tubbytwins/bumwings-kbd/v001/pcb_core52840/bumwings_v001_core.kicad_sch

## KiCad design v001/pcb_core52840/bumwings_v001_core.kicad_sch (2022-12-24)

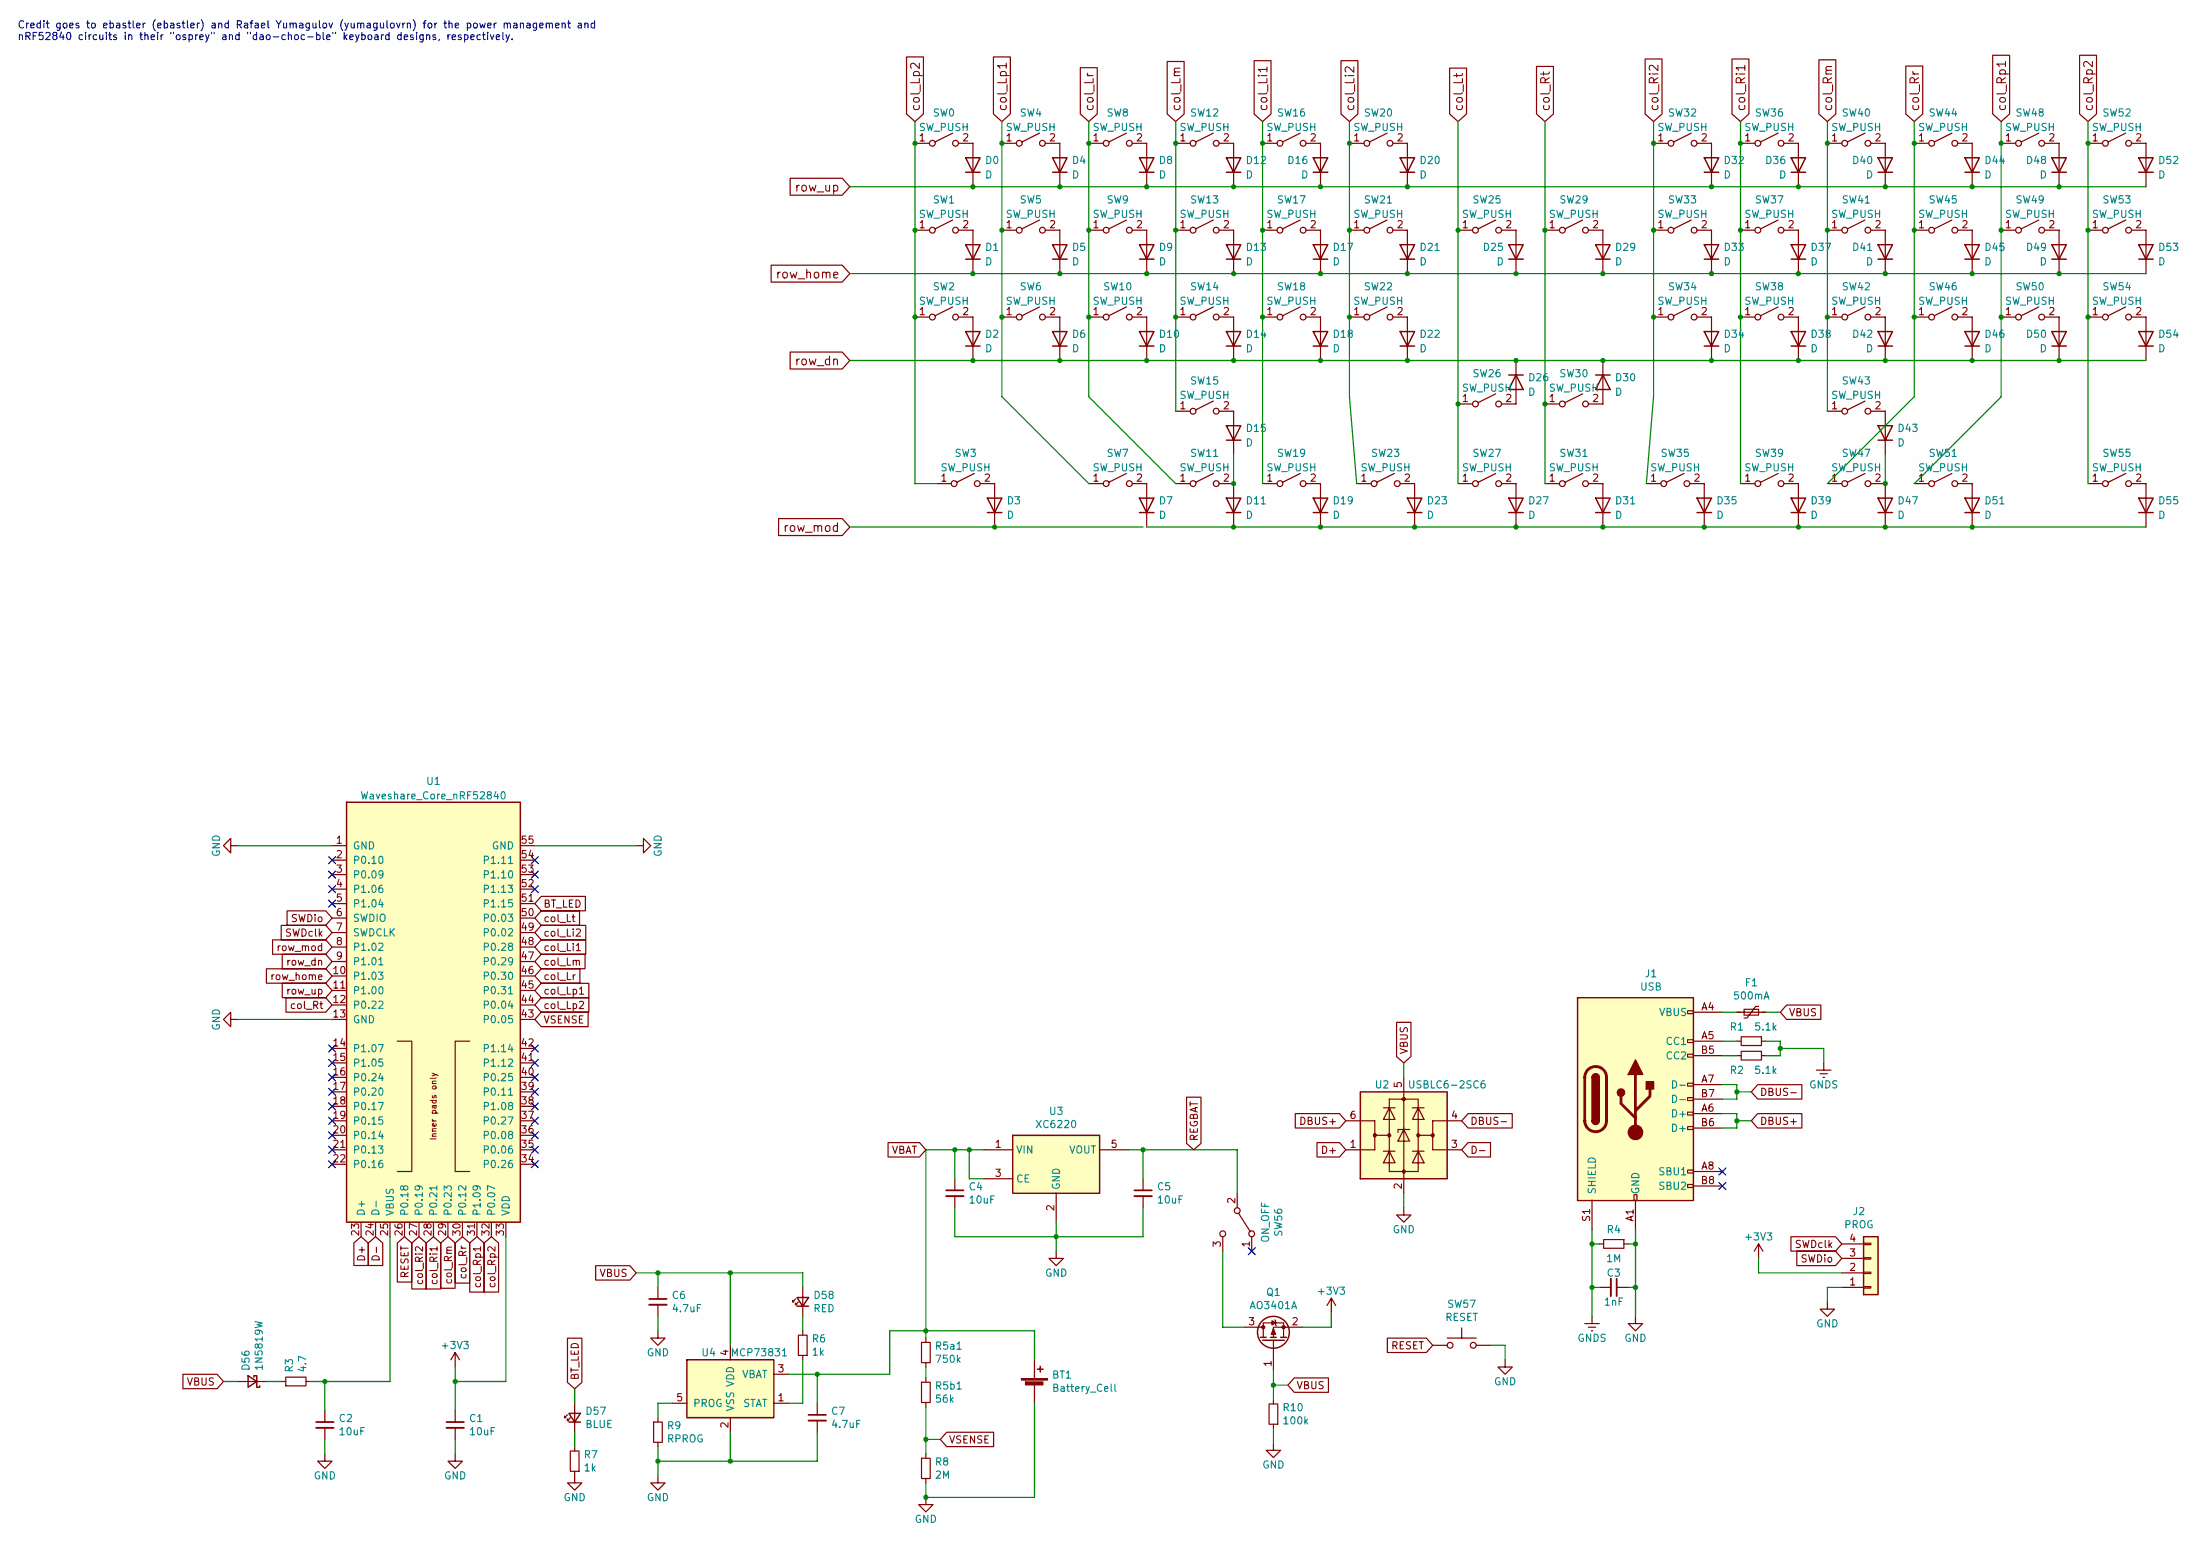
[picture p16: schematic bumwings_v001_core.kicad_sch]

Parts:
BT1: Battery_Cell; Battery
C1, C2, C4, C5: 10uF; C_1206_3216Metric_Pad1.33x1.80mm_HandSolder; LCSC C19702
C3: 1nF; C_1206_3216Metric_Pad1.33x1.80mm_HandSolder; LCSC C1588
C6, C7: 4.7uF; C_1206_3216Metric_Pad1.33x1.80mm_HandSolder; LCSC C19666
D0, D1, D2, D3, D4, D5, D6, D7, D8, D9, D10, D11, D12, D13, D14, D15, D16, D17, D18, D19, D20, D21, D22, D23, D25, D26, D27, D29, D30, D31, D32, D33, D34, D35, D36, D37, D38, D39, D40, D41, D42, D43, D44, D45, D46, D47, D48, D49, D50, D51, D52, D53, D54, D55: D; Diode_D_SOD-123
D56: 1N5819W; D_SOD-123; LCSC C169540
D57: BLUE; LED_1206_3216Metric_Pad1.42x1.75mm_HandSolder; LCSC C72041
D58: RED; LED_1206_3216Metric_Pad1.42x1.75mm_HandSolder; LCSC C2286
F1: 500mA; Fuse_1206_3216Metric_Pad1.42x1.75mm_HandSolder; LCSC C355568
J1: USB; USB-C_C168688; LCSC C168688
J2: PROG
Q1: AO3401A; SOT-23; LCSC C15127
R1, R2: 5.1k; R_1206_3216Metric_Pad1.30x1.75mm_HandSolder; LCSC C23186
R3: 4.7; R_1206_3216Metric_Pad1.30x1.75mm_HandSolder; LCSC C23164
R4: 1M; R_1206_3216Metric_Pad1.30x1.75mm_HandSolder; LCSC C22935
R5a1: 750k; R_1206_3216Metric_Pad1.30x1.75mm_HandSolder; LCSC C103828
R5b1: 56k; R_1206_3216Metric_Pad1.30x1.75mm_HandSolder; LCSC C103828
R6, R7: 1k; R_1206_3216Metric_Pad1.30x1.75mm_HandSolder; LCSC C21190
R8: 2M; R_1206_3216Metric_Pad1.30x1.75mm_HandSolder; LCSC C22976
R9: RPROG; R_1206_3216Metric_Pad1.30x1.75mm_HandSolder; LCSC C22978
R10: 100k; R_1206_3216Metric_Pad1.30x1.75mm_HandSolder; LCSC C25803
SW0, SW1, SW2, SW4, SW5, SW6, SW7, SW8, SW9, SW10, SW11, SW12, SW13, SW14, SW15, SW16, SW17, SW18, SW19, SW20, SW21, SW22, SW26, SW30, SW32, SW33, SW34, SW36, SW37, SW38, SW39, SW40, SW41, SW42, SW43, SW44, SW45, SW46, SW47, SW48, SW49, SW50, SW51, SW52, SW53, SW54: SW_PUSH; Kailh_PG1350_1u_hotswap
SW3, SW25, SW27, SW29, SW31, SW55: SW_PUSH; Kailh_PG1350_1.5u_hotswap
SW23, SW35: SW_PUSH; Kailh_PG1350_2u_stab_hotswap
SW56: ON_OFF; MSK-12C02; LCSC C431541
SW57: RESET; TS-1086E; LCSC C455276
U1: Waveshare_Core_nRF52840; Core_nRF52840
U2: USBLC6-2SC6; SOT-23-6; LCSC C558442
U3: XC6220; SOT-23-5; LCSC C86534
U4: MCP73831; SOT-23-5; LCSC C14879

Connections:
+3V3: C1.1, J2.2, Q1.2 (S), U1.33 (VDD)
BT_LED: D57.2 (A), U1.51 (P1.15)
D+: U1.23 (D+), U2.1 (I/O1)
D-: U1.24 (D-), U2.3 (I/O2)
DBUS+: J1.A6 (D+), J1.B6 (D+), U2.6 (I/O1)
DBUS-: J1.A7 (D-), J1.B7 (D-), U2.4 (I/O2)
GND: BT1.2 (-), C1.2, C2.2, C3.1, C4.2, C5.2, C6.2, C7.2, J1.A1 (GND), J1.A12 (GND), J1.B1 (GND), J1.B12 (GND), J2.1, R4.1, R7.1, R8.2, R9.2, R10.1, SW57.2, U1.1 (GND), U1.13 (GND), U1.55 (GND), U2.2 (GND), U3.2 (GND), U4.2 (VSS)
GNDS: C3.2, J1.S1 (SHIELD), R1.1, R2.1, R4.2
unnamed: C2.1, R3.2, U1.25 (VBUS)
unnamed: D0.2 (A), SW0.2 (B)
unnamed: D1.2 (A), SW1.2 (B)
unnamed: D2.2 (A), SW2.2 (B)
unnamed: D3.2 (A), SW3.2 (B)
unnamed: D4.2 (A), SW4.2 (B)
unnamed: D5.2 (A), SW5.2 (B)
unnamed: D6.2 (A), SW6.2 (B)
unnamed: D7.2 (A), SW7.2 (B)
unnamed: D8.2 (A), SW8.2 (B)
unnamed: D9.2 (A), SW9.2 (B)
unnamed: D10.2 (A), SW10.2 (B)
unnamed: D7.1 (K), D11.1 (K), D19.1 (K), D23.1 (K), D27.1 (K), D31.1 (K), D35.1 (K), D39.1 (K), D47.1 (K), D51.1 (K), D55.1 (K)
unnamed: D11.2 (A), D15.1 (K), SW11.2 (B)
unnamed: D12.2 (A), SW12.2 (B)
unnamed: D13.2 (A), SW13.2 (B)
unnamed: D14.2 (A), SW14.2 (B)
unnamed: D15.2 (A), SW15.2 (B)
unnamed: D16.2 (A), SW16.2 (B)
unnamed: D17.2 (A), SW17.2 (B)
unnamed: D18.2 (A), SW18.2 (B)
unnamed: D19.2 (A), SW19.2 (B)
unnamed: D20.2 (A), SW20.2 (B)
unnamed: D21.2 (A), SW21.2 (B)
unnamed: D22.2 (A), SW22.2 (B)
unnamed: D23.2 (A), SW23.2 (B)
unnamed: D25.2 (A), SW25.2 (B)
unnamed: D26.2 (A), SW26.2 (B)
unnamed: D27.2 (A), SW27.2 (B)
unnamed: D29.2 (A), SW29.2 (B)
unnamed: D30.2 (A), SW30.2 (B)
unnamed: D31.2 (A), SW31.2 (B)
unnamed: D32.2 (A), SW32.2 (B)
unnamed: D33.2 (A), SW33.2 (B)
unnamed: D34.2 (A), SW34.2 (B)
unnamed: D35.2 (A), SW35.2 (B)
unnamed: D36.2 (A), SW36.2 (B)
unnamed: D37.2 (A), SW37.2 (B)
unnamed: D38.2 (A), SW38.2 (B)
unnamed: D39.2 (A), SW39.2 (B)
unnamed: D40.2 (A), SW40.2 (B)
unnamed: D41.2 (A), SW41.2 (B)
unnamed: D42.2 (A), SW42.2 (B)
unnamed: D43.1 (K), D47.2 (A), SW47.2 (B)
unnamed: D43.2 (A), SW43.2 (B)
unnamed: D44.2 (A), SW44.2 (B)
unnamed: D45.2 (A), SW45.2 (B)
unnamed: D46.2 (A), SW46.2 (B)
unnamed: D48.2 (A), SW48.2 (B)
unnamed: D49.2 (A), SW49.2 (B)
unnamed: D50.2 (A), SW50.2 (B)
unnamed: D51.2 (A), SW51.2 (B)
unnamed: D52.2 (A), SW52.2 (B)
unnamed: D53.2 (A), SW53.2 (B)
unnamed: D54.2 (A), SW54.2 (B)
unnamed: D55.2 (A), SW55.2 (B)
unnamed: D56.1 (K), R3.1
unnamed: D57.1 (K), R7.2
unnamed: D58.1 (K), R6.2
unnamed: F1.2, J1.A4 (VBUS), J1.A9 (VBUS), J1.B4 (VBUS), J1.B9 (VBUS)
unnamed: J1.A5 (CC1), R1.2
unnamed: J1.B5 (CC2), R2.2
unnamed: Q1.3 (D), SW56.3 (C)
unnamed: R5a1.2, R5b1.1
unnamed: R6.1, U4.1 (STAT)
unnamed: R9.1, U4.5 (PROG)
REGBAT: C5.1, SW56.2 (B), U3.5 (VOUT)
RESET: SW57.1, U1.26 (P0.18)
SWDclk: J2.4, U1.7 (SWDCLK)
SWDio: J2.3, U1.6 (SWDIO)
VBAT: BT1.1 (+), C4.1, C7.1, R5a1.1, U3.1 (VIN), U3.3 (CE), U4.3 (VBAT)
VBUS: C6.1, D56.2 (A), D58.2 (A), F1.1, Q1.1 (G), R10.2, U2.5 (VBUS), U4.4 (VDD)
VSENSE: R5b1.2, R8.1, U1.43 (P0.05)
col_Li1: SW16.1 (A), SW17.1 (A), SW18.1 (A), SW19.1 (A), U1.48 (P0.28)
col_Li2: SW20.1 (A), SW21.1 (A), SW22.1 (A), SW23.1 (A), U1.49 (P0.02)
col_Lm: SW12.1 (A), SW13.1 (A), SW14.1 (A), SW15.1 (A), U1.47 (P0.29)
col_Lp1: SW4.1 (A), SW5.1 (A), SW6.1 (A), SW7.1 (A), U1.45 (P0.31)
col_Lp2: SW0.1 (A), SW1.1 (A), SW2.1 (A), SW3.1 (A), U1.44 (P0.04)
col_Lr: SW8.1 (A), SW9.1 (A), SW10.1 (A), SW11.1 (A), U1.46 (P0.30)
col_Lt: SW25.1 (A), SW26.1 (A), SW27.1 (A), U1.50 (P0.03)
col_Ri1: SW36.1 (A), SW37.1 (A), SW38.1 (A), SW39.1 (A), U1.28 (P0.21)
col_Ri2: SW32.1 (A), SW33.1 (A), SW34.1 (A), SW35.1 (A), U1.27 (P0.19)
col_Rm: SW40.1 (A), SW41.1 (A), SW42.1 (A), SW43.1 (A), U1.29 (P0.23)
col_Rp1: SW48.1 (A), SW49.1 (A), SW50.1 (A), SW51.1 (A), U1.31 (P1.09)
col_Rp2: SW52.1 (A), SW53.1 (A), SW54.1 (A), SW55.1 (A), U1.32 (P0.07)
col_Rr: SW44.1 (A), SW45.1 (A), SW46.1 (A), SW47.1 (A), U1.30 (P0.12)
col_Rt: SW29.1 (A), SW30.1 (A), SW31.1 (A), U1.12 (P0.22)
row_dn: D2.1 (K), D6.1 (K), D10.1 (K), D14.1 (K), D18.1 (K), D22.1 (K), D26.1 (K), D30.1 (K), D34.1 (K), D38.1 (K), D42.1 (K), D46.1 (K), D50.1 (K), D54.1 (K), U1.9 (P1.01)
row_home: D1.1 (K), D5.1 (K), D9.1 (K), D13.1 (K), D17.1 (K), D21.1 (K), D25.1 (K), D29.1 (K), D33.1 (K), D37.1 (K), D41.1 (K), D45.1 (K), D49.1 (K), D53.1 (K), U1.10 (P1.03)
row_mod: D3.1 (K), U1.8 (P1.02)
row_up: D0.1 (K), D4.1 (K), D8.1 (K), D12.1 (K), D16.1 (K), D20.1 (K), D32.1 (K), D36.1 (K), D40.1 (K), D44.1 (K), D48.1 (K), D52.1 (K), U1.11 (P1.00)

Notes on the sheet:
Credit goes to ebastler (ebastler) and Rafael Yumagulov (yumagulovrn) for the power management and nRF52840 circuits in their "osprey" and "dao-choc-ble" keyboard designs, respectively.
