tubbytwins/bumwings-kbd/v001/pcb_rp2040zero/bumwings_v001.kicad_sch

## KiCad design v001/pcb_rp2040zero/bumwings_v001.kicad_sch (2022-11-17)

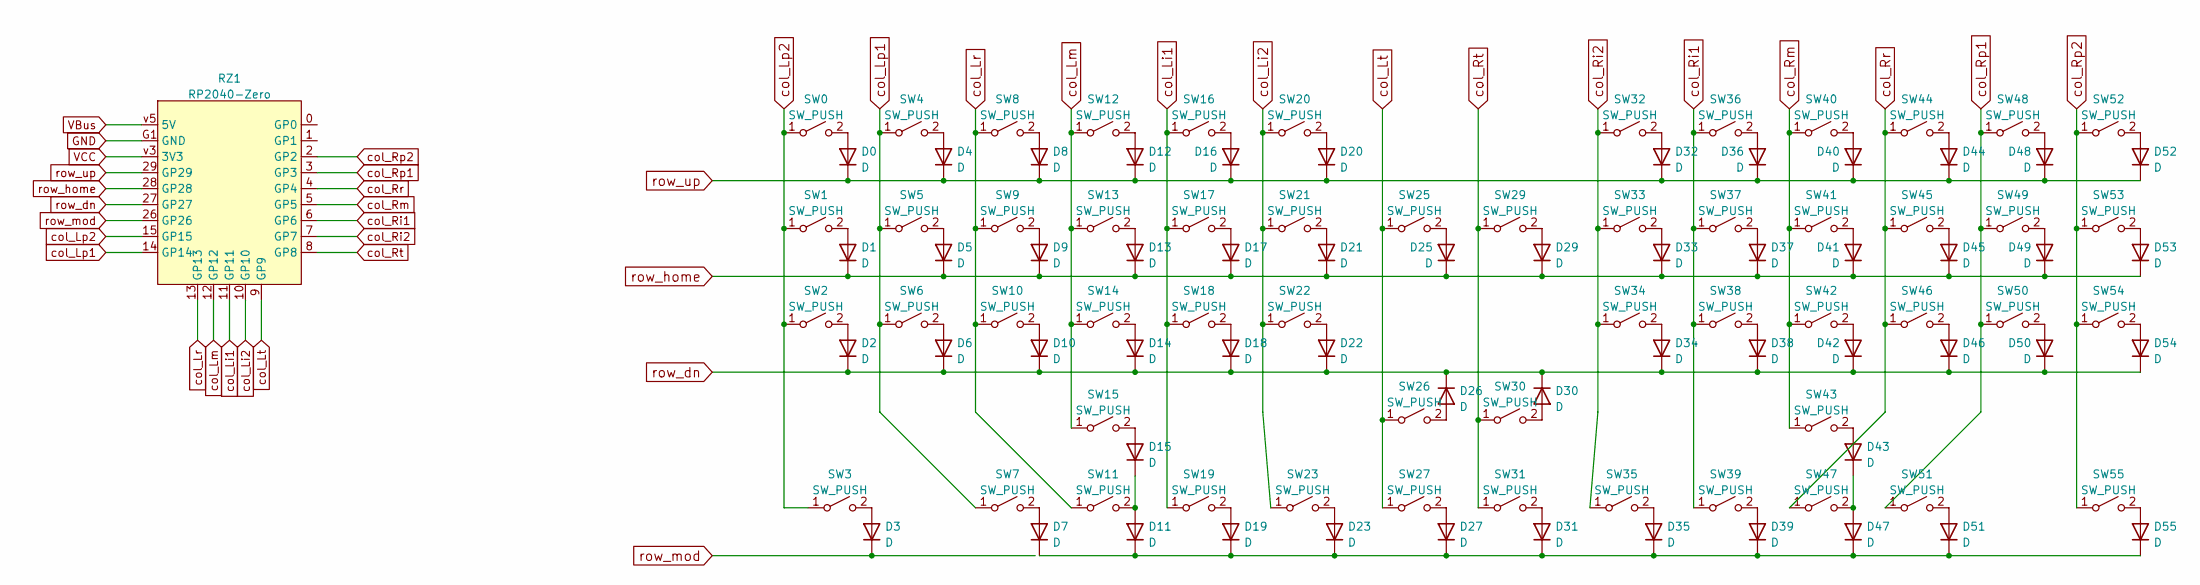
[picture p17: schematic bumwings_v001.kicad_sch]

Parts:
D0, D1, D2, D3, D4, D5, D6, D7, D8, D9, D10, D11, D12, D13, D14, D15, D16, D17, D18, D19, D20, D21, D22, D23, D25, D26, D27, D29, D30, D31, D32, D33, D34, D35, D36, D37, D38, D39, D40, D41, D42, D43, D44, D45, D46, D47, D48, D49, D50, D51, D52, D53, D54, D55: D; Diode_D_SOD-123
RZ1: RP2040-Zero
SW0, SW1, SW2, SW4, SW5, SW6, SW7, SW8, SW9, SW10, SW11, SW12, SW13, SW14, SW15, SW16, SW17, SW18, SW19, SW20, SW21, SW22, SW26, SW30, SW32, SW33, SW34, SW36, SW37, SW38, SW39, SW40, SW41, SW42, SW43, SW44, SW45, SW46, SW47, SW48, SW49, SW50, SW51, SW52, SW53, SW54: SW_PUSH; Kailh_PG1350_1u_hotswap
SW3, SW25, SW27, SW29, SW31, SW55: SW_PUSH; Kailh_PG1350_1.5u_hotswap
SW23, SW35: SW_PUSH; Kailh_PG1350_2u_stab_hotswap

Connections:
GND: RZ1.G1 (GND)
unnamed: D0.2 (A), SW0.2 (B)
unnamed: D1.2 (A), SW1.2 (B)
unnamed: D2.2 (A), SW2.2 (B)
unnamed: D3.2 (A), SW3.2 (B)
unnamed: D4.2 (A), SW4.2 (B)
unnamed: D5.2 (A), SW5.2 (B)
unnamed: D6.2 (A), SW6.2 (B)
unnamed: D7.2 (A), SW7.2 (B)
unnamed: D8.2 (A), SW8.2 (B)
unnamed: D9.2 (A), SW9.2 (B)
unnamed: D10.2 (A), SW10.2 (B)
unnamed: D7.1 (K), D11.1 (K), D19.1 (K), D23.1 (K), D27.1 (K), D31.1 (K), D35.1 (K), D39.1 (K), D47.1 (K), D51.1 (K), D55.1 (K)
unnamed: D11.2 (A), D15.1 (K), SW11.2 (B)
unnamed: D12.2 (A), SW12.2 (B)
unnamed: D13.2 (A), SW13.2 (B)
unnamed: D14.2 (A), SW14.2 (B)
unnamed: D15.2 (A), SW15.2 (B)
unnamed: D16.2 (A), SW16.2 (B)
unnamed: D17.2 (A), SW17.2 (B)
unnamed: D18.2 (A), SW18.2 (B)
unnamed: D19.2 (A), SW19.2 (B)
unnamed: D20.2 (A), SW20.2 (B)
unnamed: D21.2 (A), SW21.2 (B)
unnamed: D22.2 (A), SW22.2 (B)
unnamed: D23.2 (A), SW23.2 (B)
unnamed: D25.2 (A), SW25.2 (B)
unnamed: D26.2 (A), SW26.2 (B)
unnamed: D27.2 (A), SW27.2 (B)
unnamed: D29.2 (A), SW29.2 (B)
unnamed: D30.2 (A), SW30.2 (B)
unnamed: D31.2 (A), SW31.2 (B)
unnamed: D32.2 (A), SW32.2 (B)
unnamed: D33.2 (A), SW33.2 (B)
unnamed: D34.2 (A), SW34.2 (B)
unnamed: D35.2 (A), SW35.2 (B)
unnamed: D36.2 (A), SW36.2 (B)
unnamed: D37.2 (A), SW37.2 (B)
unnamed: D38.2 (A), SW38.2 (B)
unnamed: D39.2 (A), SW39.2 (B)
unnamed: D40.2 (A), SW40.2 (B)
unnamed: D41.2 (A), SW41.2 (B)
unnamed: D42.2 (A), SW42.2 (B)
unnamed: D43.1 (K), D47.2 (A), SW47.2 (B)
unnamed: D43.2 (A), SW43.2 (B)
unnamed: D44.2 (A), SW44.2 (B)
unnamed: D45.2 (A), SW45.2 (B)
unnamed: D46.2 (A), SW46.2 (B)
unnamed: D48.2 (A), SW48.2 (B)
unnamed: D49.2 (A), SW49.2 (B)
unnamed: D50.2 (A), SW50.2 (B)
unnamed: D51.2 (A), SW51.2 (B)
unnamed: D52.2 (A), SW52.2 (B)
unnamed: D53.2 (A), SW53.2 (B)
unnamed: D54.2 (A), SW54.2 (B)
unnamed: D55.2 (A), SW55.2 (B)
VBus: RZ1.v5 (5V)
VCC: RZ1.v3 (3V3)
col_Li1: RZ1.11 (GP11), SW16.1 (A), SW17.1 (A), SW18.1 (A), SW19.1 (A)
col_Li2: RZ1.10 (GP10), SW20.1 (A), SW21.1 (A), SW22.1 (A), SW23.1 (A)
col_Lm: RZ1.12 (GP12), SW12.1 (A), SW13.1 (A), SW14.1 (A), SW15.1 (A)
col_Lp1: RZ1.14 (GP14), SW4.1 (A), SW5.1 (A), SW6.1 (A), SW7.1 (A)
col_Lp2: RZ1.15 (GP15), SW0.1 (A), SW1.1 (A), SW2.1 (A), SW3.1 (A)
col_Lr: RZ1.13 (GP13), SW8.1 (A), SW9.1 (A), SW10.1 (A), SW11.1 (A)
col_Lt: RZ1.9 (GP9), SW25.1 (A), SW26.1 (A), SW27.1 (A)
col_Ri1: RZ1.6 (GP6), SW36.1 (A), SW37.1 (A), SW38.1 (A), SW39.1 (A)
col_Ri2: RZ1.7 (GP7), SW32.1 (A), SW33.1 (A), SW34.1 (A), SW35.1 (A)
col_Rm: RZ1.5 (GP5), SW40.1 (A), SW41.1 (A), SW42.1 (A), SW43.1 (A)
col_Rp1: RZ1.3 (GP3), SW48.1 (A), SW49.1 (A), SW50.1 (A), SW51.1 (A)
col_Rp2: RZ1.2 (GP2), SW52.1 (A), SW53.1 (A), SW54.1 (A), SW55.1 (A)
col_Rr: RZ1.4 (GP4), SW44.1 (A), SW45.1 (A), SW46.1 (A), SW47.1 (A)
col_Rt: RZ1.8 (GP8), SW29.1 (A), SW30.1 (A), SW31.1 (A)
row_dn: D2.1 (K), D6.1 (K), D10.1 (K), D14.1 (K), D18.1 (K), D22.1 (K), D26.1 (K), D30.1 (K), D34.1 (K), D38.1 (K), D42.1 (K), D46.1 (K), D50.1 (K), D54.1 (K), RZ1.27 (GP27)
row_home: D1.1 (K), D5.1 (K), D9.1 (K), D13.1 (K), D17.1 (K), D21.1 (K), D25.1 (K), D29.1 (K), D33.1 (K), D37.1 (K), D41.1 (K), D45.1 (K), D49.1 (K), D53.1 (K), RZ1.28 (GP28)
row_mod: D3.1 (K), RZ1.26 (GP26)
row_up: D0.1 (K), D4.1 (K), D8.1 (K), D12.1 (K), D16.1 (K), D20.1 (K), D32.1 (K), D36.1 (K), D40.1 (K), D44.1 (K), D48.1 (K), D52.1 (K), RZ1.29 (GP29)
