tubbytwins/bumwings-kbd/v001R/pcb_R64_nano_sd/bumwings_v001R64_nano_sd.kicad_sch

## KiCad design v001R/pcb_R64_nano_sd/bumwings_v001R64_nano_sd.kicad_sch (2023-09-30)

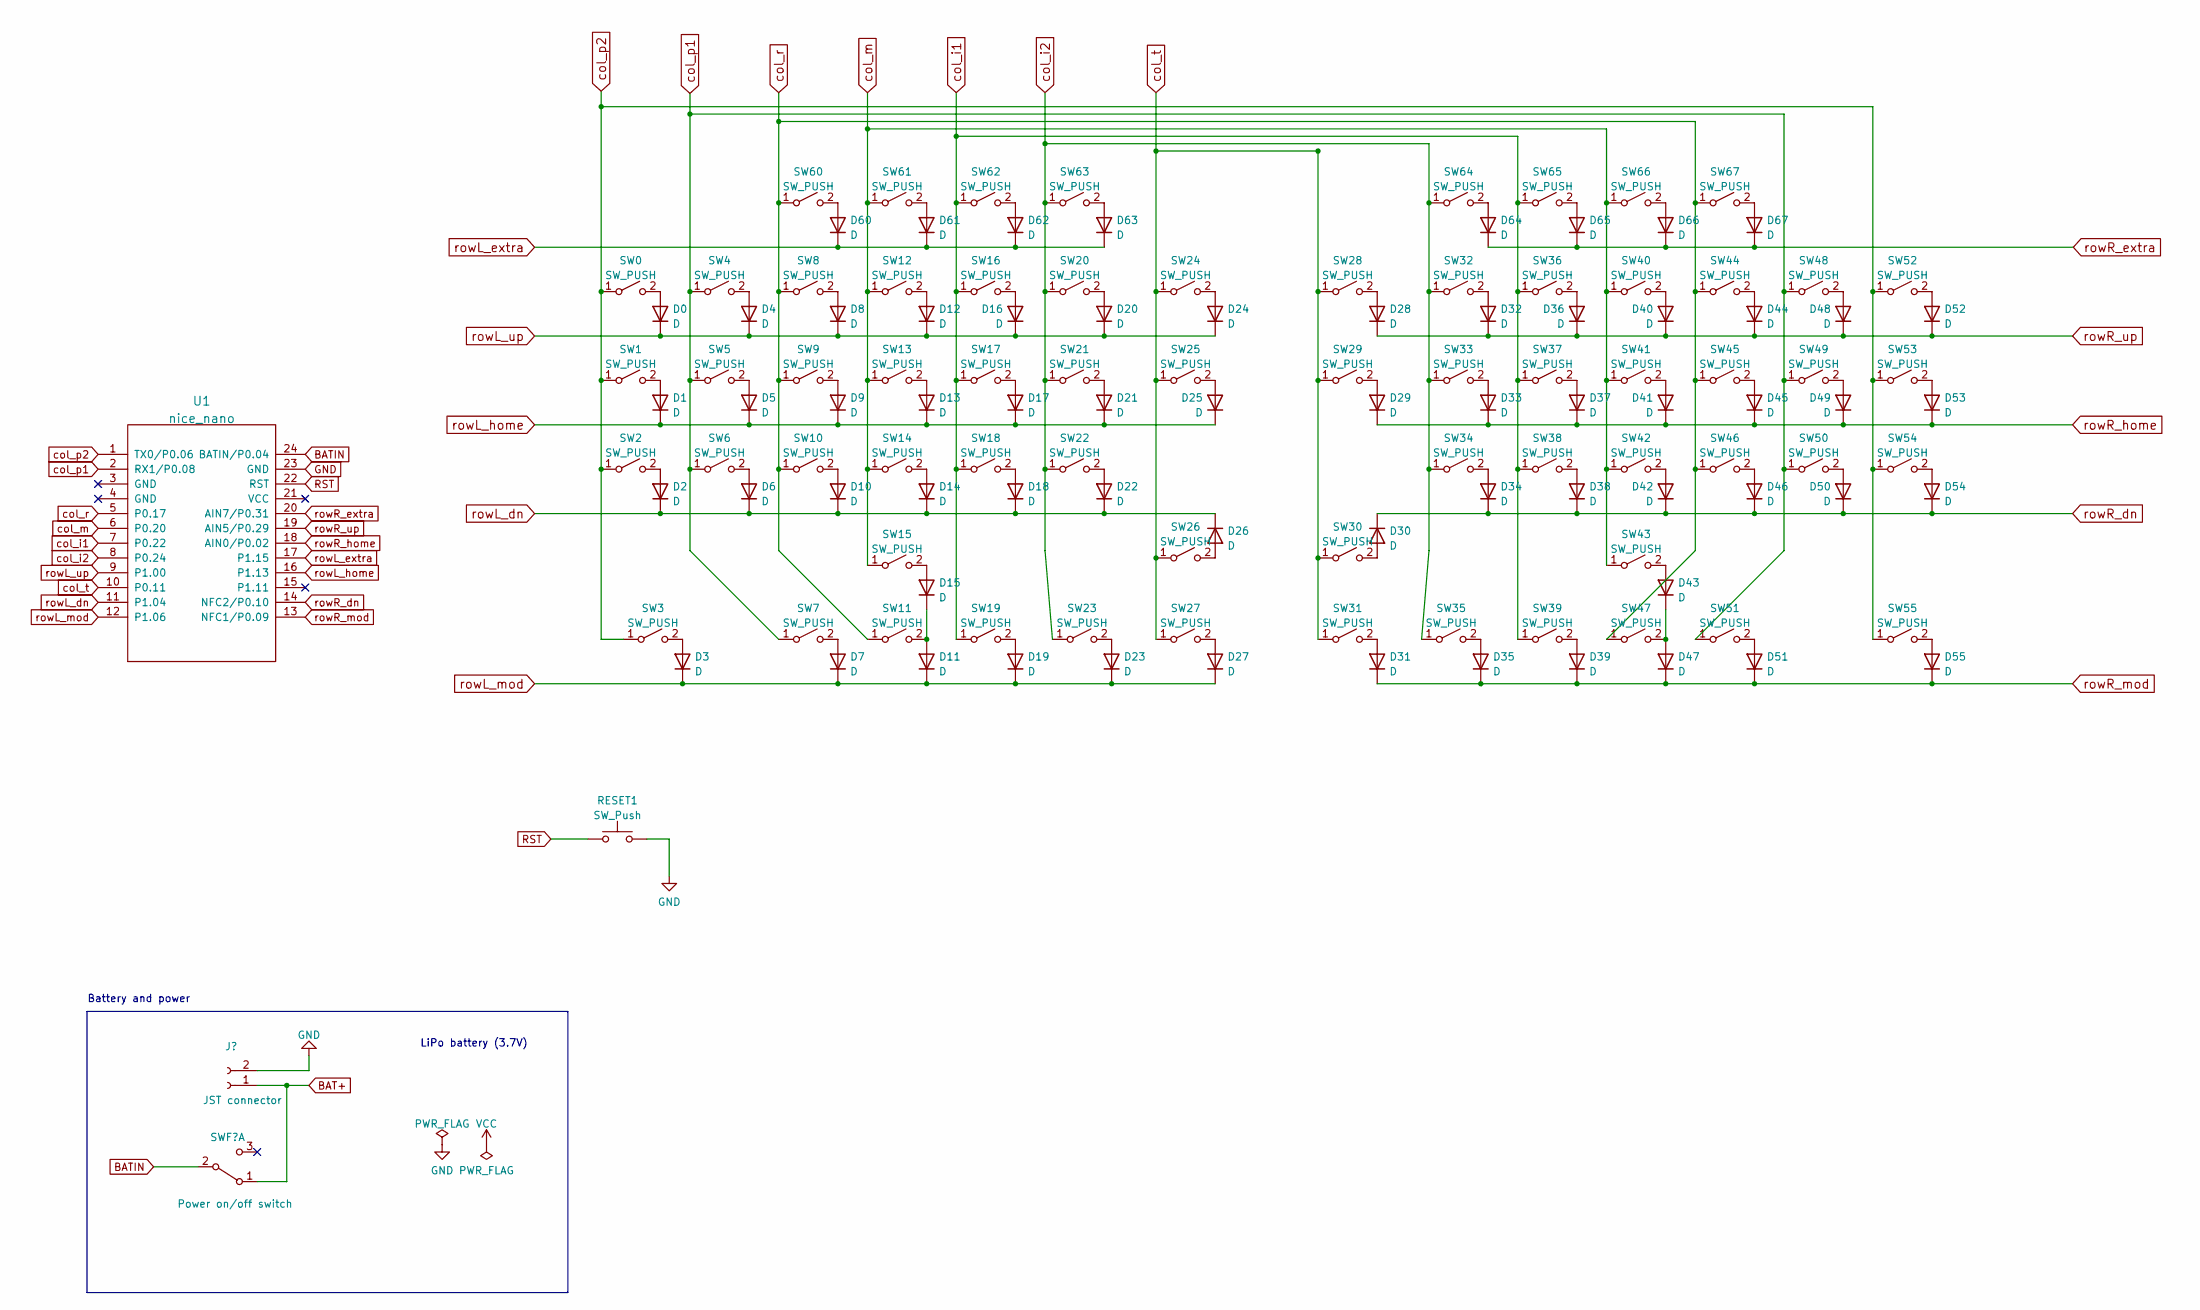
[picture p18: schematic bumwings_v001R64_nano_sd.kicad_sch]

Parts:
D0, D1, D2, D3, D4, D5, D6, D7, D8, D9, D10, D11, D12, D13, D14, D15, D16, D17, D18, D19, D20, D21, D22, D23, D24, D25, D26, D27, D28, D29, D30, D31, D32, D33, D34, D35, D36, D37, D38, D39, D40, D41, D42, D43, D44, D45, D46, D47, D48, D49, D50, D51, D52, D53, D54, D55, D60, D61, D62, D63, D64, D65, D66, D67: D; Diode_D_SOD-123
RESET1: SW_Push; b3u1000p
SW0, SW1, SW2, SW4, SW5, SW6, SW7, SW8, SW9, SW10, SW11, SW12, SW13, SW14, SW15, SW16, SW17, SW18, SW19, SW20, SW21, SW22, SW24, SW26, SW28, SW30, SW32, SW33, SW34, SW36, SW37, SW38, SW39, SW40, SW41, SW42, SW43, SW44, SW45, SW46, SW47, SW48, SW49, SW50, SW51, SW52, SW53, SW54, SW60, SW61, SW62, SW63, SW64, SW65, SW66, SW67: SW_PUSH; Kailh_PG1350_1u_hotswap
SW3, SW25, SW27, SW29, SW31, SW55: SW_PUSH; Kailh_PG1350_1.5u_hotswap
SW23, SW35: SW_PUSH; Kailh_PG1350_2u_stab_hotswap
U1: nice_nano; nice-nano-no-rev

Connections:
BATIN: U1.24 (BATIN/P0.04)
GND: U1.23 (GND)
unnamed: D0.2 (A), SW0.2 (B)
unnamed: D1.2 (A), SW1.2 (B)
unnamed: D2.2 (A), SW2.2 (B)
unnamed: D3.2 (A), SW3.2 (B)
unnamed: D4.2 (A), SW4.2 (B)
unnamed: D5.2 (A), SW5.2 (B)
unnamed: D6.2 (A), SW6.2 (B)
unnamed: D7.2 (A), SW7.2 (B)
unnamed: D8.2 (A), SW8.2 (B)
unnamed: D9.2 (A), SW9.2 (B)
unnamed: D10.2 (A), SW10.2 (B)
unnamed: D11.2 (A), D15.1 (K), SW11.2 (B)
unnamed: D12.2 (A), SW12.2 (B)
unnamed: D13.2 (A), SW13.2 (B)
unnamed: D14.2 (A), SW14.2 (B)
unnamed: D15.2 (A), SW15.2 (B)
unnamed: D16.2 (A), SW16.2 (B)
unnamed: D17.2 (A), SW17.2 (B)
unnamed: D18.2 (A), SW18.2 (B)
unnamed: D19.2 (A), SW19.2 (B)
unnamed: D20.2 (A), SW20.2 (B)
unnamed: D21.2 (A), SW21.2 (B)
unnamed: D22.2 (A), SW22.2 (B)
unnamed: D23.2 (A), SW23.2 (B)
unnamed: D24.2 (A), SW24.2 (B)
unnamed: D25.2 (A), SW25.2 (B)
unnamed: D26.2 (A), SW26.2 (B)
unnamed: D27.2 (A), SW27.2 (B)
unnamed: D28.2 (A), SW28.2 (B)
unnamed: D29.2 (A), SW29.2 (B)
unnamed: D30.2 (A), SW30.2 (B)
unnamed: D31.2 (A), SW31.2 (B)
unnamed: D32.2 (A), SW32.2 (B)
unnamed: D33.2 (A), SW33.2 (B)
unnamed: D34.2 (A), SW34.2 (B)
unnamed: D35.2 (A), SW35.2 (B)
unnamed: D36.2 (A), SW36.2 (B)
unnamed: D37.2 (A), SW37.2 (B)
unnamed: D38.2 (A), SW38.2 (B)
unnamed: D39.2 (A), SW39.2 (B)
unnamed: D40.2 (A), SW40.2 (B)
unnamed: D41.2 (A), SW41.2 (B)
unnamed: D42.2 (A), SW42.2 (B)
unnamed: D43.1 (K), D47.2 (A), SW47.2 (B)
unnamed: D43.2 (A), SW43.2 (B)
unnamed: D44.2 (A), SW44.2 (B)
unnamed: D45.2 (A), SW45.2 (B)
unnamed: D46.2 (A), SW46.2 (B)
unnamed: D48.2 (A), SW48.2 (B)
unnamed: D49.2 (A), SW49.2 (B)
unnamed: D50.2 (A), SW50.2 (B)
unnamed: D51.2 (A), SW51.2 (B)
unnamed: D52.2 (A), SW52.2 (B)
unnamed: D53.2 (A), SW53.2 (B)
unnamed: D54.2 (A), SW54.2 (B)
unnamed: D55.2 (A), SW55.2 (B)
unnamed: D60.2 (A), SW60.2 (B)
unnamed: D61.2 (A), SW61.2 (B)
unnamed: D62.2 (A), SW62.2 (B)
unnamed: D63.2 (A), SW63.2 (B)
unnamed: D64.2 (A), SW64.2 (B)
unnamed: D65.2 (A), SW65.2 (B)
unnamed: D66.2 (A), SW66.2 (B)
unnamed: D67.2 (A), SW67.2 (B)
RST: RESET1.1, U1.22 (RST)
col_i1: SW16.1 (A), SW17.1 (A), SW18.1 (A), SW19.1 (A), SW36.1 (A), SW37.1 (A), SW38.1 (A), SW39.1 (A), SW62.1 (A), SW65.1 (A), U1.7 (P0.22)
col_i2: SW20.1 (A), SW21.1 (A), SW22.1 (A), SW23.1 (A), SW32.1 (A), SW33.1 (A), SW34.1 (A), SW35.1 (A), SW63.1 (A), SW64.1 (A), U1.8 (P0.24)
col_m: SW12.1 (A), SW13.1 (A), SW14.1 (A), SW15.1 (A), SW40.1 (A), SW41.1 (A), SW42.1 (A), SW43.1 (A), SW61.1 (A), SW66.1 (A), U1.6 (P0.20)
col_p1: SW4.1 (A), SW5.1 (A), SW6.1 (A), SW7.1 (A), SW48.1 (A), SW49.1 (A), SW50.1 (A), SW51.1 (A), U1.2 (RX1/P0.08)
col_p2: SW0.1 (A), SW1.1 (A), SW2.1 (A), SW3.1 (A), SW52.1 (A), SW53.1 (A), SW54.1 (A), SW55.1 (A), U1.1 (TX0/P0.06)
col_r: SW8.1 (A), SW9.1 (A), SW10.1 (A), SW11.1 (A), SW44.1 (A), SW45.1 (A), SW46.1 (A), SW47.1 (A), SW60.1 (A), SW67.1 (A), U1.5 (P0.17)
col_t: SW24.1 (A), SW25.1 (A), SW26.1 (A), SW27.1 (A), SW28.1 (A), SW29.1 (A), SW30.1 (A), SW31.1 (A), U1.10 (P0.11)
rowL_dn: D2.1 (K), D6.1 (K), D10.1 (K), D14.1 (K), D18.1 (K), D22.1 (K), D26.1 (K), U1.11 (P1.04)
rowL_extra: D60.1 (K), D61.1 (K), D62.1 (K), D63.1 (K), U1.17 (P1.15)
rowL_home: D1.1 (K), D5.1 (K), D9.1 (K), D13.1 (K), D17.1 (K), D21.1 (K), D25.1 (K), U1.16 (P1.13)
rowL_mod: D3.1 (K), D7.1 (K), D11.1 (K), D19.1 (K), D23.1 (K), D27.1 (K), U1.12 (P1.06)
rowL_up: D0.1 (K), D4.1 (K), D8.1 (K), D12.1 (K), D16.1 (K), D20.1 (K), D24.1 (K), U1.9 (P1.00)
rowR_dn: D30.1 (K), D34.1 (K), D38.1 (K), D42.1 (K), D46.1 (K), D50.1 (K), D54.1 (K), U1.14 (NFC2/P0.10)
rowR_extra: D64.1 (K), D65.1 (K), D66.1 (K), D67.1 (K), U1.20 (AIN7/P0.31)
rowR_home: D29.1 (K), D33.1 (K), D37.1 (K), D41.1 (K), D45.1 (K), D49.1 (K), D53.1 (K), U1.18 (AIN0/P0.02)
rowR_mod: D31.1 (K), D35.1 (K), D39.1 (K), D47.1 (K), D51.1 (K), D55.1 (K), U1.13 (NFC1/P0.09)
rowR_up: D28.1 (K), D32.1 (K), D36.1 (K), D40.1 (K), D44.1 (K), D48.1 (K), D52.1 (K), U1.19 (AIN5/P0.29)

Notes on the sheet:
LiPo battery (3.7V)
Battery and power
